skiselev/isa-fdc/images/ISA_FDC-Assembled_Board-0.9-800px.jpg

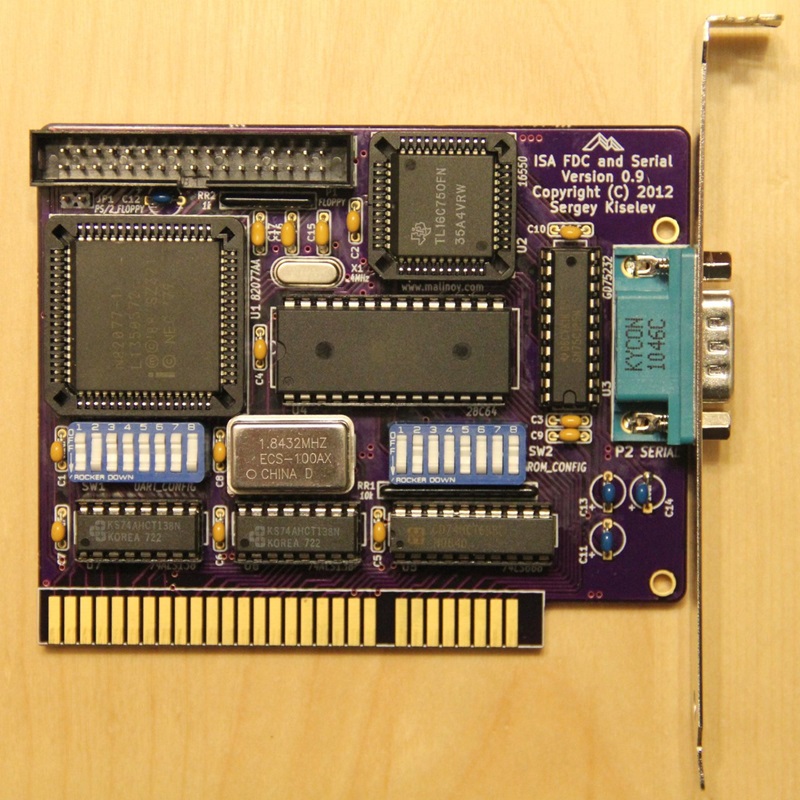
images/ISA_FDC-Assembled_Board-0.9-800px.jpg
